Gcerpa01/Bloom/Schematic and PCB/PCB Files/Etchable PDF/PCB Design_etch_silk_bottom.pdf

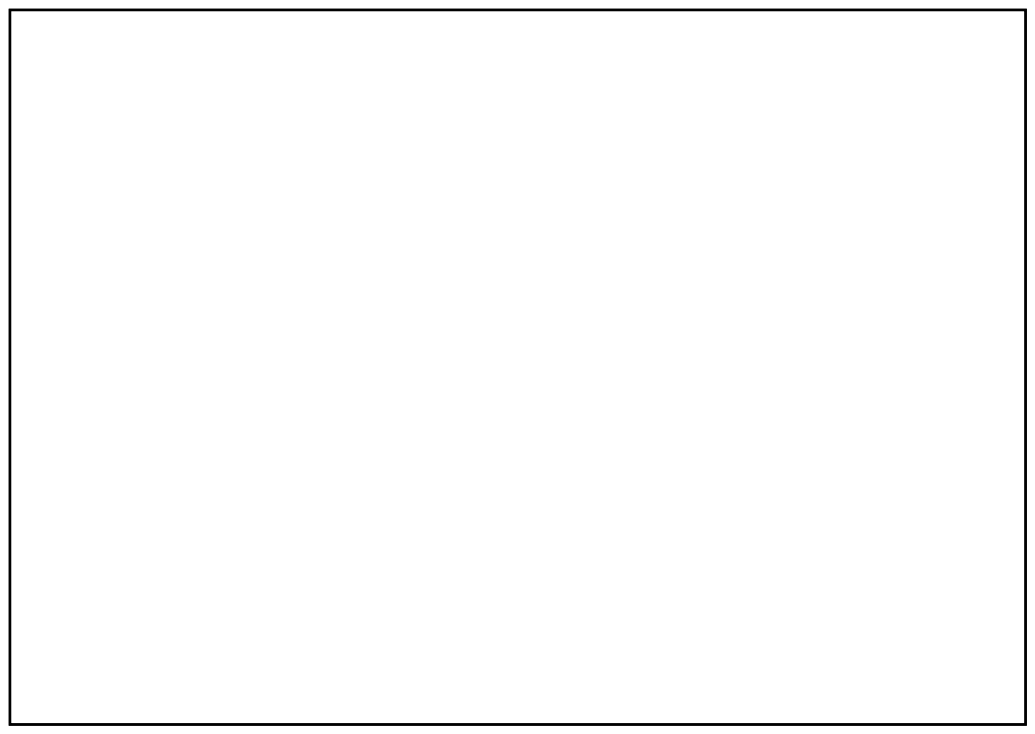
[picture p10: page 1]
