Gcerpa01/Bloom/Schematic and PCB/PCB Files/Etchable PDF/PCB Design_etch_silk_bottom_mirror.pdf

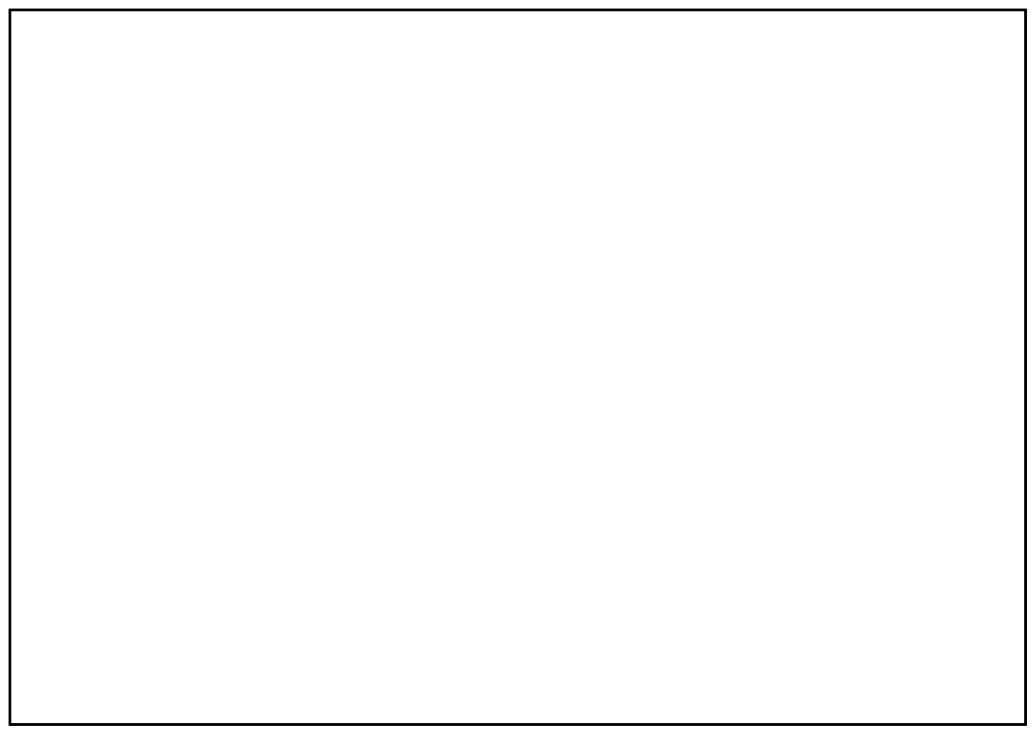
[picture p11: page 1]
