Gcerpa01/Bloom/Schematic and PCB/PCB Files/Etchable PDF/PCB Design_etch_silk_top.pdf

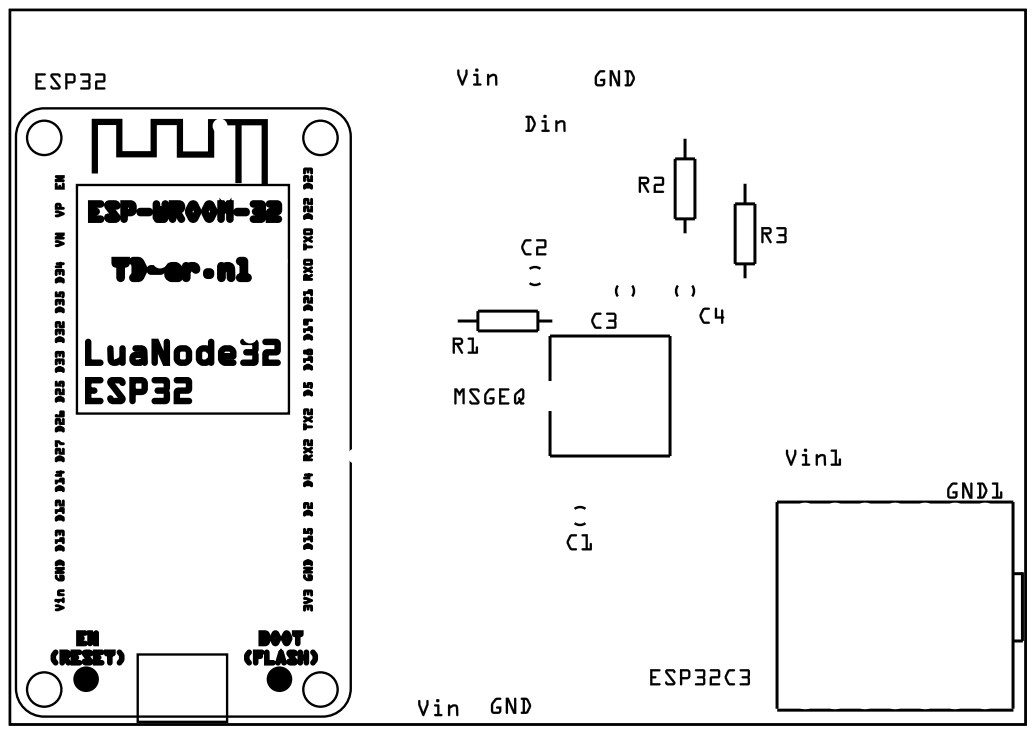
[picture p12: page 1]
