Gcerpa01/Bloom/Schematic and PCB/PCB Files/Etchable PDF/PCB Design_etch_silk_top_mirror.pdf

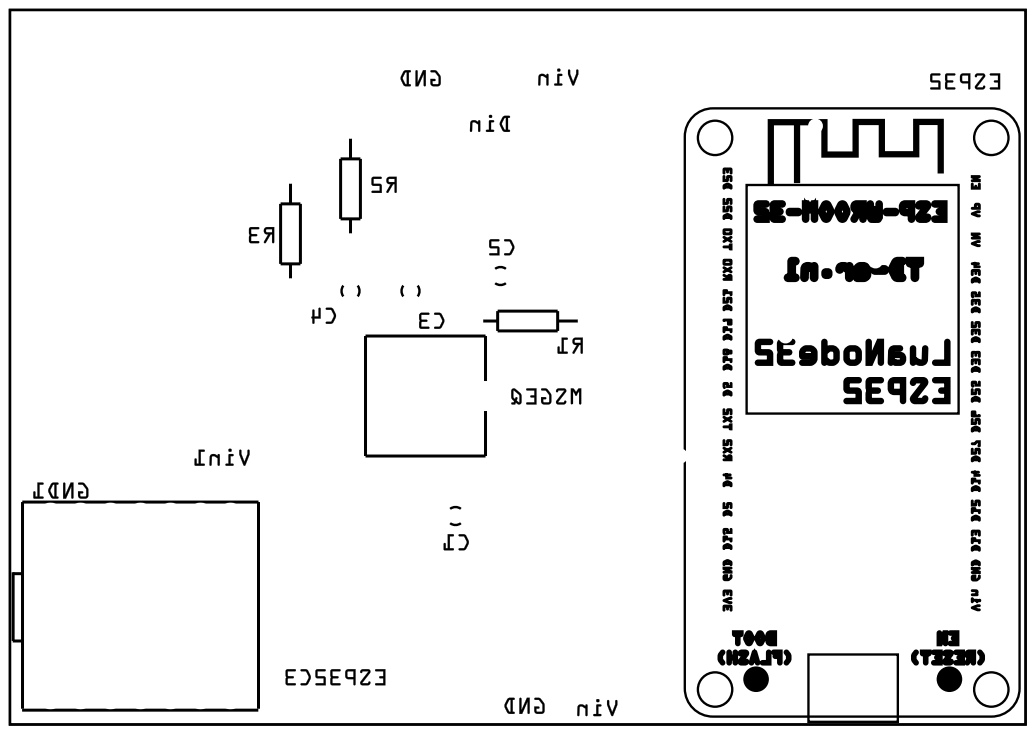
[picture p13: page 1]
